heonaliu/bear-magotchi/Images/PCB_Images/3D_Board.png

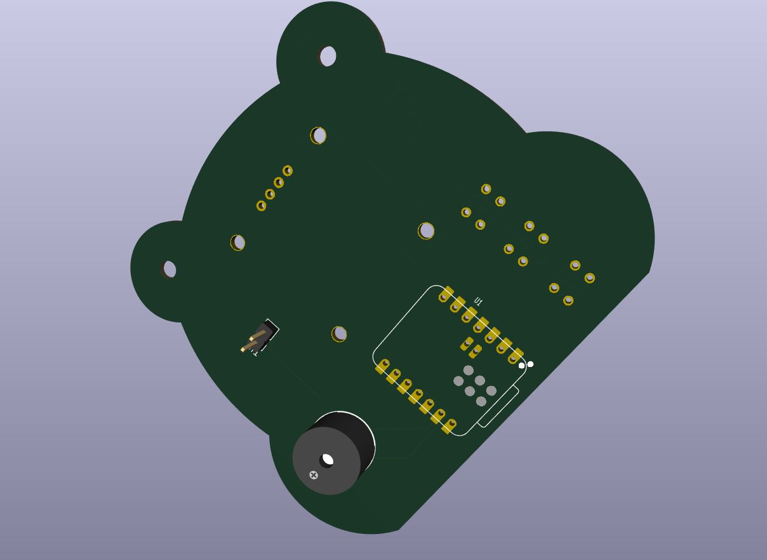
Images/PCB_Images/3D_Board.png
